IAD-ZHDK/ShifterBit/Code/_MQTT.ino

#include <ESP8266WiFi.h>
#include <MQTTClient.h>

WiFiClient mqtt_net;
MQTTClient mqtt_client;

void mqtt_setup() {
  mqtt_client.begin(config_mqtt_broker, mqtt_net);
  
  Serial.println("Connecting to shiftr.io...");
  if (mqtt_client.connect("arduino", "try", "try")) {
    Serial.println("Connected!");

    if(config_subscribe) {
      mqtt_client.subscribe(config_subscribe_topic);
    }
  } else {
    Serial.println("Cot connected!");
  }
}

void mqtt_loop() {
  mqtt_client.loop();
}

void messageReceived(String topic, String payload, char * bytes, unsigned int length) {
  Serial.print("incoming: ");
  Serial.print(topic);
  Serial.print(" - ");
  Serial.print(payload);
  Serial.println();
}
